NJIT-Highlander-Racing-Electrical/BajaDAS/Photos/IMG_1266.JPEG

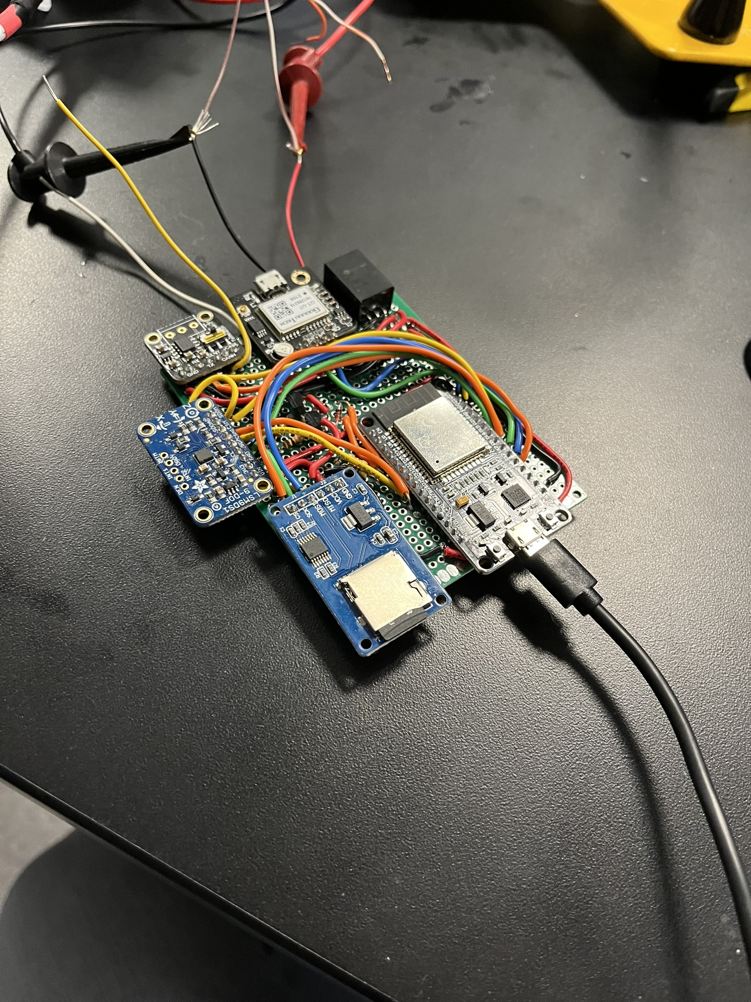
Photos/IMG_1266.JPEG
