NJIT-Highlander-Racing-Electrical/BajaDAS/Photos/IMG_1277.JPEG

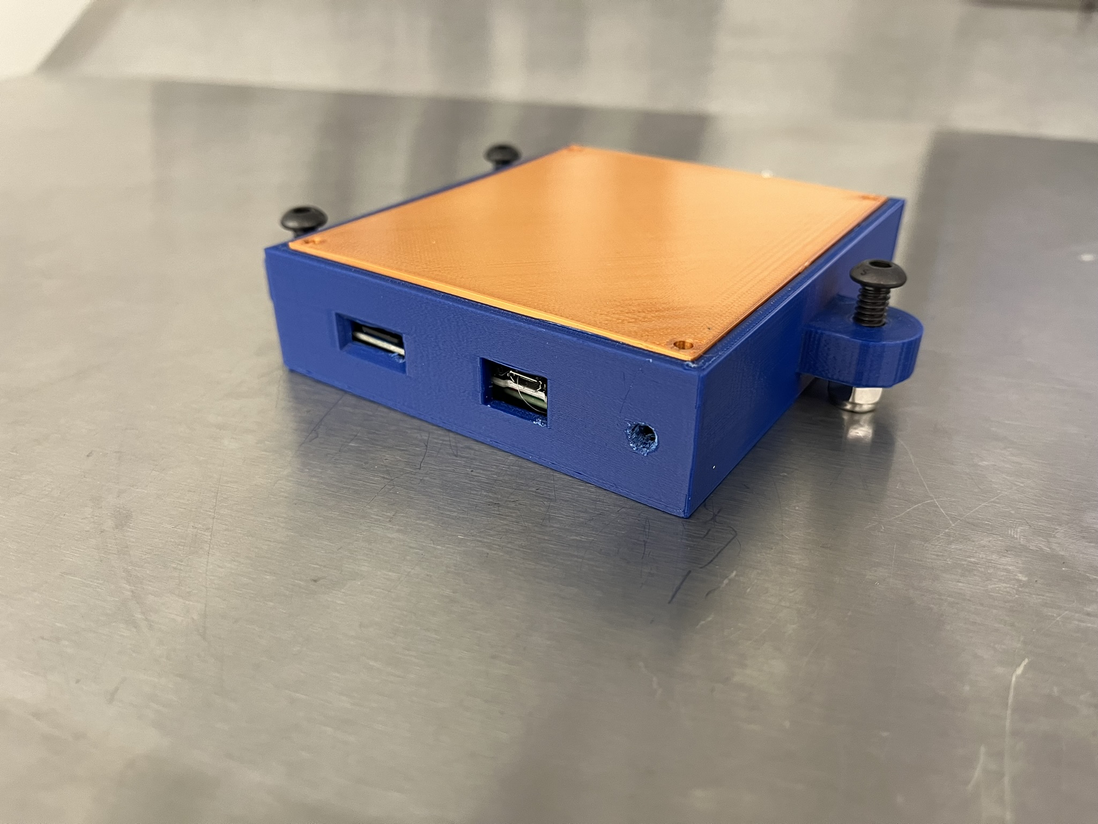
Photos/IMG_1277.JPEG
