NJIT-Highlander-Racing-Electrical/BajaDAS/Photos/IMG_1278.JPEG

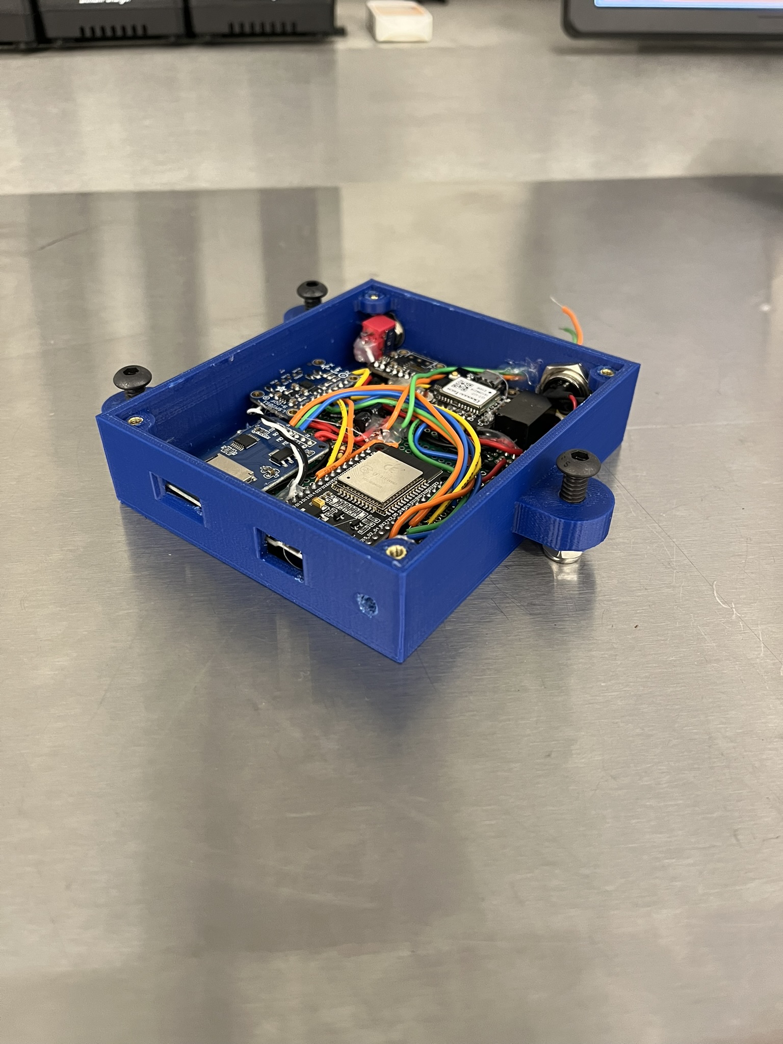
Photos/IMG_1278.JPEG
