NJIT-Highlander-Racing-Electrical/BajaDAS/Photos/IMG_1314.JPEG

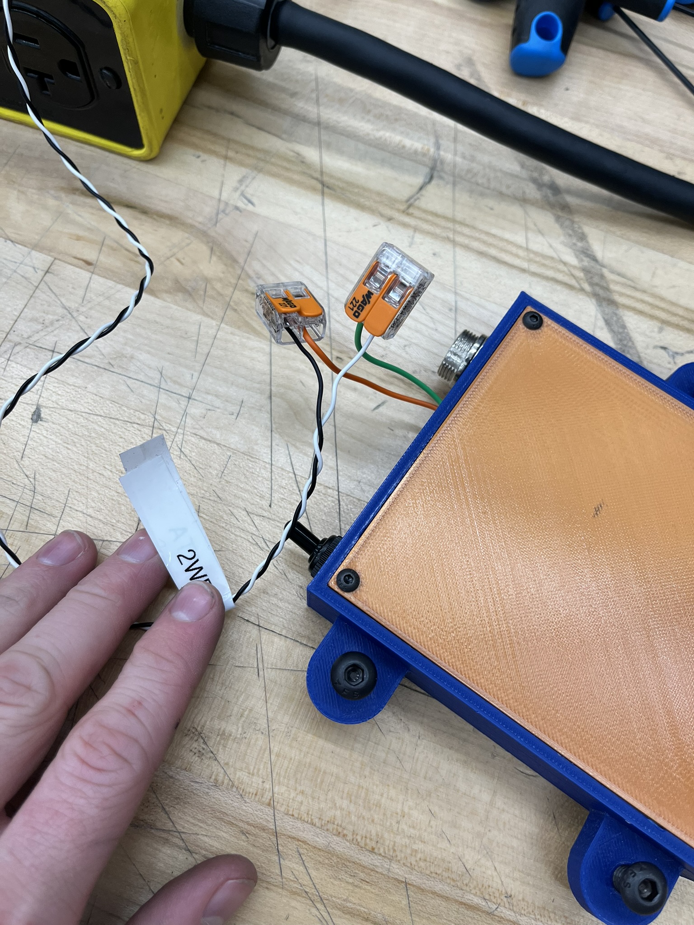
Photos/IMG_1314.JPEG
