NJIT-Highlander-Racing-Electrical/BajaDAS/Photos/IMG_1247.JPG

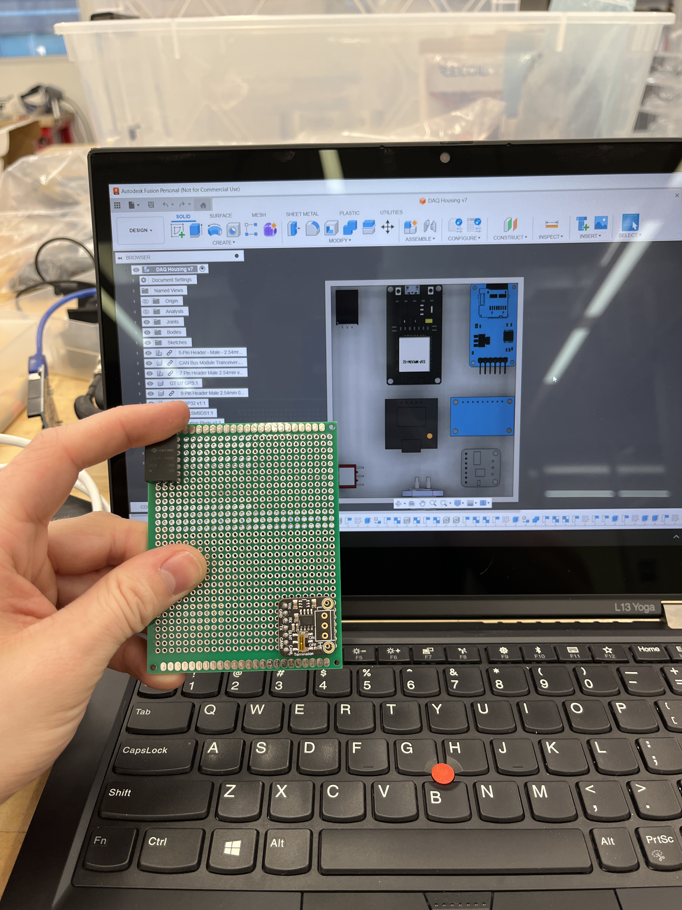
Photos/IMG_1247.JPG
